stevenchadburrow/RPi02W-Emulators/Emulators/keyboard.c

#include <stdio.h>
#include <stdlib.h>
#include <fcntl.h>
#include <linux/input.h>
#include <unistd.h>

int main()
{
	system("echo \"0000000000000\" > keyboard1.val");
	system("echo \"0000000000000\" > keyboard2.val");

	char button[13];

	for (int i=0; i<13; i++) button[i] = '0';

	char string[256];

	for (int i=0; i<256; i++) string[i] = 0;

	system("lsusb | grep -i 'key' > usb.val");

	FILE *input = NULL;

	input = fopen("usb.val", "rt");
	if (!input)
	{
		printf("Cannot open usb.val\n");
		return 0;
	}

	char buffer[1];
	int bytes = fscanf(input, "%c", &buffer);

	fclose(input);

	system("rm usb.val");

	if (bytes <= 0) return 1; // if no keyboard present, exit

	int keys_fd;
    struct input_event keys_ev;

	keys_fd = open("/dev/input/event0", O_RDONLY);

	if (keys_fd > 0)
	{
		while (1)
		{
			read(keys_fd, &keys_ev, sizeof(struct input_event));

			//printf("%d %d\n", keys_ev.code, keys_ev.value); // just for testing

			if (keys_ev.code == 1) // escape for MENU
			{
				button[0] = (char)((unsigned char)keys_ev.value + '0');
			}
			else if (keys_ev.code == 17) // w for UP
			{
				button[1] = (char)((unsigned char)keys_ev.value + '0');
			}
			else if (keys_ev.code == 31) // s for DOWN
			{
				button[2] = (char)((unsigned char)keys_ev.value + '0');
			}
			else if (keys_ev.code == 30) // a for LEFT
			{
				button[3] = (char)((unsigned char)keys_ev.value + '0');
			}
			else if (keys_ev.code == 32) // d for RIGHT
			{
				button[4] = (char)((unsigned char)keys_ev.value + '0');
			}
			else if (keys_ev.code == 14) // backspace for SELECT
			{
				button[5] = (char)((unsigned char)keys_ev.value + '0');
			}
			else if (keys_ev.code == 28) // return for START
			{
				button[6] = (char)((unsigned char)keys_ev.value + '0');
			}
			else if (keys_ev.code == 37) // k for A
			{
				button[7] = (char)((unsigned char)keys_ev.value + '0');
			}
			else if (keys_ev.code == 36) // j for B
			{
				button[8] = (char)((unsigned char)keys_ev.value + '0');
			}
			else if (keys_ev.code == 23) // i for X
			{
				button[9] = (char)((unsigned char)keys_ev.value + '0');
			}
			else if (keys_ev.code == 22) // u for Y
			{
				button[10] = (char)((unsigned char)keys_ev.value + '0');
			}
			else if (keys_ev.code == 35) // h for L
			{
				button[11] = (char)((unsigned char)keys_ev.value + '0');
			}
			else if (keys_ev.code == 38) // l for R
			{
				button[12] = (char)((unsigned char)keys_ev.value + '0');
			}

			for (int i=0; i<256; i++) string[i] = 0;
	
			sprintf(string, "echo \"%c%c%c%c%c%c%c%c%c%c%c%c%c\" > keyboard1.val",
				button[0], button[1], button[2], button[3],
				button[4], button[5], button[6], button[7], button[8],
				button[9], button[10], button[11], button[12]);

			//printf("%s\n", string);
			system(string);

			for (int i=0; i<256; i++) string[i] = 0;
	
			sprintf(string, "echo \"%c%c%c%c%c%c%c%c%c%c%c%c%c\" > keyboard2.val",
				button[0], button[1], button[2], button[3],
				button[4], button[5], button[6], button[7], button[8],
				button[9], button[10], button[11], button[12]);

			//printf("%s\n", string);
			system(string);

			//if (button[0] != '0') break;
		}
	}

	if (keys_fd > 0) close(keys_fd);

    return 0;
}
